tjko/fanpico/images/fanpico-0200-v1.0.jpg

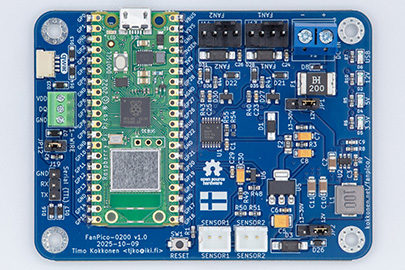
images/fanpico-0200-v1.0.jpg
