tjko/fanpico/images/fanpico-0804D-large.jpg

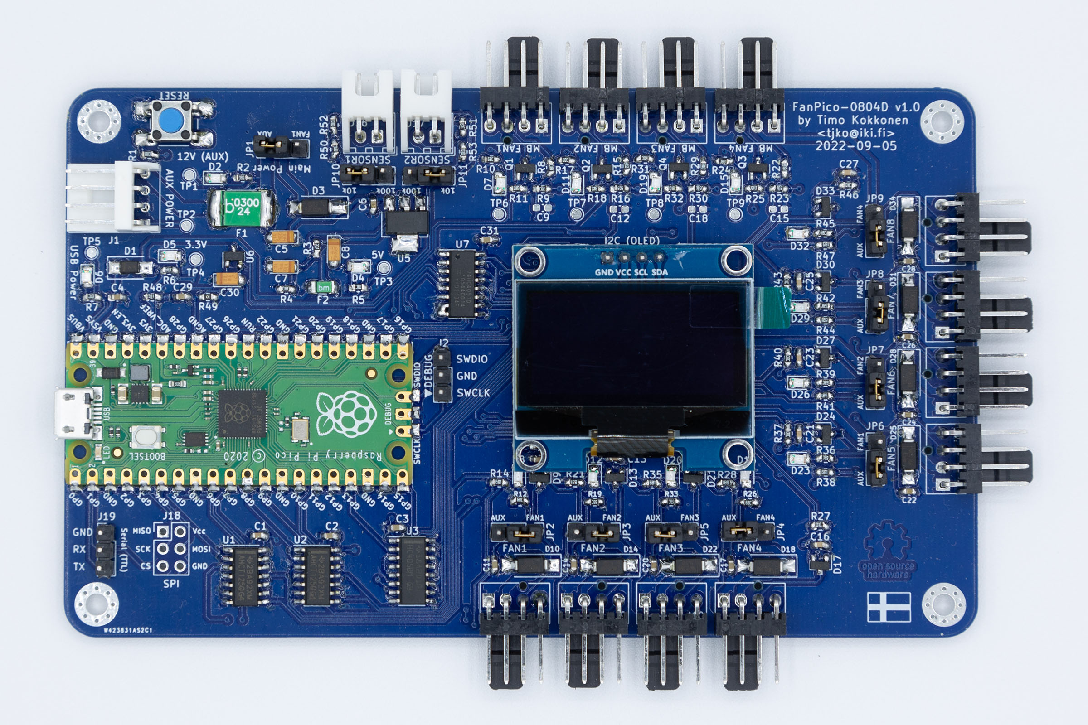
images/fanpico-0804D-large.jpg
