tjko/fanpico/images/fanpico-0804D-v1.2c-large.jpg

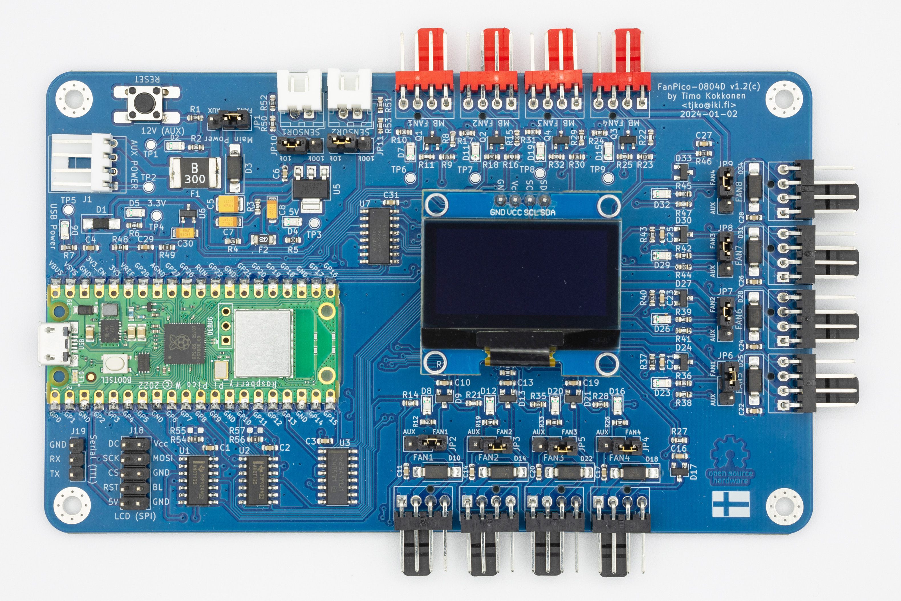
images/fanpico-0804D-v1.2c-large.jpg
