tjko/fanpico/images/fanpico-prototype.jpg

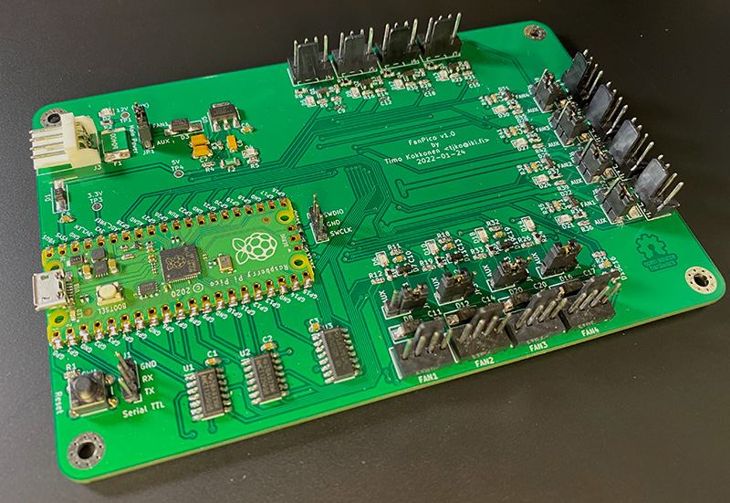
images/fanpico-prototype.jpg
