tjko/fanpico/images/oled-128x64-layout.jpg

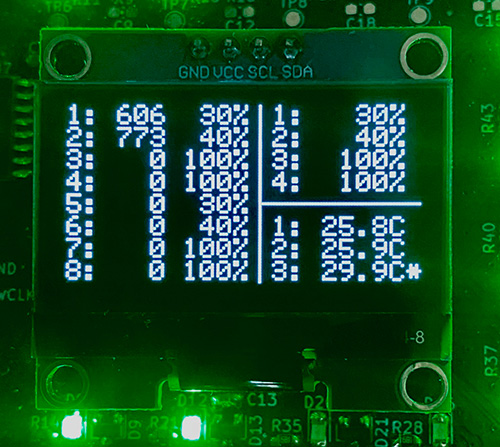
images/oled-128x64-layout.jpg
