tjko/fanpico/images/oled-128x128-layout.jpg

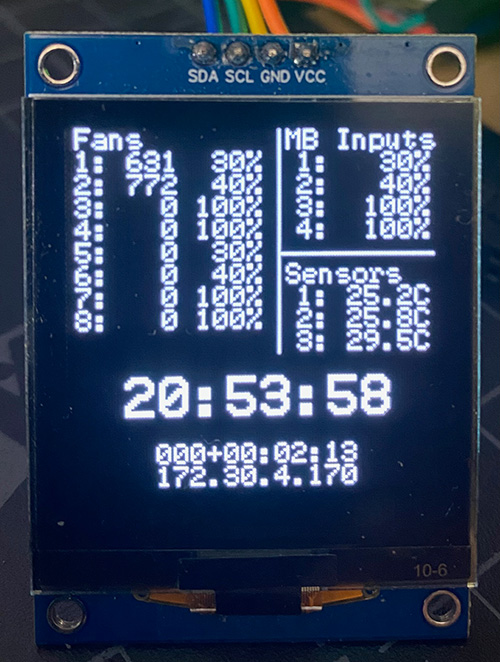
images/oled-128x128-layout.jpg
