tjko/fanpico/images/theme-default-320x240-small.jpg

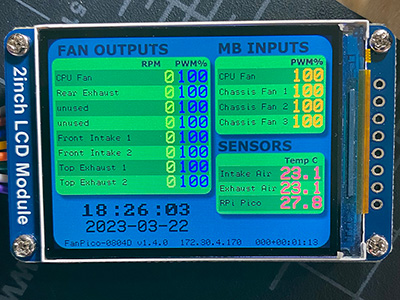
images/theme-default-320x240-small.jpg
