tjko/fanpico/src/themes/default-320x240.png

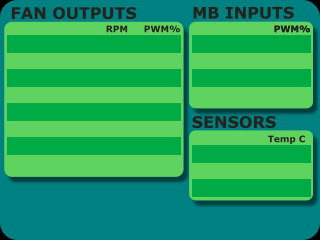
src/themes/default-320x240.png
