tjko/fanpico/src/themes/default-480x320.png

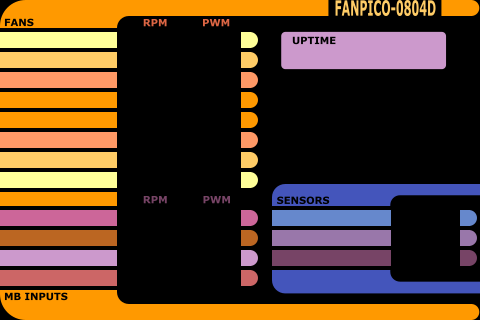
src/themes/default-480x320.png
