tjko/fanpico/src/fanpico_fsdata.c

#include "lwip/apps/fs.h"

static const unsigned char data__404_html[] = {

    /* "/404.html" (10 chars) */
    0x2f,0x34,0x30,0x34,0x2e,0x68,0x74,0x6d,0x6c,0x00,0x00,0x00,

    /* "HTTP/1.0 404 File not found" (29 chars) */
    0x48,0x54,0x54,0x50,0x2f,0x31,0x2e,0x30,0x20,0x34,0x30,0x34,0x20,0x46,0x69,0x6c,
    0x65,0x20,0x6e,0x6f,0x74,0x20,0x66,0x6f,0x75,0x6e,0x64,0x0d,0x0a,

    /* "Server: lwIP/2.2.1 (FanPico)" (30 chars) */
    0x53,0x65,0x72,0x76,0x65,0x72,0x3a,0x20,0x6c,0x77,0x49,0x50,0x2f,0x32,0x2e,0x32,
    0x2e,0x31,0x20,0x28,0x46,0x61,0x6e,0x50,0x69,0x63,0x6f,0x29,0x0d,0x0a,

    /* "Content-Length: 521" (21 chars) */
    0x43,0x6f,0x6e,0x74,0x65,0x6e,0x74,0x2d,0x4c,0x65,0x6e,0x67,0x74,0x68,0x3a,0x20,
    0x35,0x32,0x31,0x0d,0x0a,

    /* "Last-Modified: Tue, 22 Sep 2026 06:35:00 GMT" (46 chars) */
    0x4c,0x61,0x73,0x74,0x2d,0x4d,0x6f,0x64,0x69,0x66,0x69,0x65,0x64,0x3a,0x20,0x54,
    0x75,0x65,0x2c,0x20,0x32,0x32,0x20,0x53,0x65,0x70,0x20,0x32,0x30,0x32,0x36,0x20,
    0x30,0x36,0x3a,0x33,0x35,0x3a,0x30,0x30,0x20,0x47,0x4d,0x54,0x0d,0x0a,

    /* "Content-Type: text/html" (27 chars) */
    0x43,0x6f,0x6e,0x74,0x65,0x6e,0x74,0x2d,0x54,0x79,0x70,0x65,0x3a,0x20,0x74,0x65,
    0x78,0x74,0x2f,0x68,0x74,0x6d,0x6c,0x0d,0x0a,0x0d,0x0a,

    /* raw file data (521 bytes) */
    0x3c,0x68,0x74,0x6d,0x6c,0x3e,0x0a,0x3c,0x68,0x65,0x61,0x64,0x3e,0x3c,0x74,0x69,
    0x74,0x6c,0x65,0x3e,0x46,0x61,0x6e,0x50,0x69,0x63,0x6f,0x3a,0x20,0x45,0x72,0x72,
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
    0x6f,0x2d,0x73,0x74,0x6f,0x72,0x65,0x2c,0x20,0x6e,0x6f,0x2d,0x63,0x61,0x63,0x68,
    0x65,0x2c,0x20,0x6d,0x75,0x73,0x74,0x2d,0x72,0x65,0x76,0x61,0x6c,0x69,0x64,0x61,
    0x74,0x65,0x0d,0x0a,

    /* "Expires: 0" (12) chars) */
    0x45,0x78,0x70,0x69,0x72,0x65,0x73,0x3a,0x20,0x30,0x0d,0x0a,

    /* "Pragma: no-cache" (18) chars) */
    0x50,0x72,0x61,0x67,0x6d,0x61,0x3a,0x20,0x6e,0x6f,0x2d,0x63,0x61,0x63,0x68,0x65,
    0x0d,0x0a,

    /* "Content-Type: application/json" (34 chars) */
    0x43,0x6f,0x6e,0x74,0x65,0x6e,0x74,0x2d,0x54,0x79,0x70,0x65,0x3a,0x20,0x61,0x70,
    0x70,0x6c,0x69,0x63,0x61,0x74,0x69,0x6f,0x6e,0x2f,0x6a,0x73,0x6f,0x6e,0x0d,0x0a,
    0x0d,0x0a,

    /* raw file data (17 bytes) */
    0x3c,0x21,0x2d,0x2d,0x23,0x6a,0x73,0x6f,0x6e,0x73,0x74,0x61,0x74,0x2d,0x2d,0x3e,
    0x0a,
};

const struct fsdata_file file__404_html[] = { {
    NULL,
    data__404_html,
    data__404_html + 12,
    sizeof(data__404_html) - 12,
    FS_FILE_FLAGS_HEADER_INCLUDED | FS_FILE_FLAGS_HEADER_PERSISTENT,
}};

const struct fsdata_file file__fanpico_css[] = { {
    file__404_html,
    data__fanpico_css,
    data__fanpico_css + 16,
    sizeof(data__fanpico_css) - 16,
    FS_FILE_FLAGS_HEADER_INCLUDED | FS_FILE_FLAGS_HEADER_PERSISTENT,
}};

const struct fsdata_file file__img_fanpico_icon_png[] = { {
    file__fanpico_css,
    data__img_fanpico_icon_png,
    data__img_fanpico_icon_png + 24,
    sizeof(data__img_fanpico_icon_png) - 24,
    FS_FILE_FLAGS_HEADER_INCLUDED | FS_FILE_FLAGS_HEADER_PERSISTENT,
}};

const struct fsdata_file file__img_fanpico_png[] = { {
    file__img_fanpico_icon_png,
    data__img_fanpico_png,
    data__img_fanpico_png + 20,
    sizeof(data__img_fanpico_png) - 20,
    FS_FILE_FLAGS_HEADER_INCLUDED | FS_FILE_FLAGS_HEADER_PERSISTENT,
}};

const struct fsdata_file file__index_shtml[] = { {
    file__img_fanpico_png,
    data__index_shtml,
    data__index_shtml + 16,
    sizeof(data__index_shtml) - 16,
    FS_FILE_FLAGS_HEADER_INCLUDED | FS_FILE_FLAGS_SSI,
}};

const struct fsdata_file file__status_csv[] = { {
    file__index_shtml,
    data__status_csv,
    data__status_csv + 12,
    sizeof(data__status_csv) - 12,
    FS_FILE_FLAGS_HEADER_INCLUDED | FS_FILE_FLAGS_SSI,
}};

const struct fsdata_file file__status_json[] = { {
    file__status_csv,
    data__status_json,
    data__status_json + 16,
    sizeof(data__status_json) - 16,
    FS_FILE_FLAGS_HEADER_INCLUDED | FS_FILE_FLAGS_SSI,
}};

#define FS_ROOT file__status_json
#define FS_NUMFILES 7
