tjko/fanpico/src/display_lcd.c

/* display_lcd.c
   Copyright (C) 2022-2023 Timo Kokkonen <tjko@iki.fi>

   SPDX-License-Identifier: GPL-3.0-or-later

   This file is part of FanPico.

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
   You should have received a copy of the GNU General Public License
   along with FanPico. If not, see <https://www.gnu.org/licenses/>.
*/

#include <stdio.h>
#include <stdlib.h>
#include <string.h>
#include <math.h>
#include <assert.h>
#include "pico/stdlib.h"

#include "bb_spi_lcd.h"
#include "fanpico.h"

#if LCD_DISPLAY

static SPILCD lcd;
static uint8_t lcd_found = 0;


/* Macros for converting RGB888 colorspace to RGB565 */

/* Convert 24bit color space to 16bit color space.  */
#define RGB565(rgb) (uint16_t)( ((rgb & 0xf80000) >> 8) | ((rgb & 0xfc00) >> 5) | ((rgb & 0xf8) >> 3) )
/* Generate 16bit color from 8bit RGB components. */
#define RGB565C(r, g, b) (uint16_t)( ((r & 0xf8) << 8) | ((g & 0xfc) << 3) | ((b & 0xf8) >> 3) )


struct lcd_type {
	const char* name;
	int dtype;
	int flags;
	int orientation;
	int32_t spi_freq;
	const uint8_t *custom_init;
	uint32_t custom_init_len;
	int invert_offset;
	int rgb_offset;
};

enum display_field_types {
	INVALID_FIELDTYPE = 0,
	FAN,
	MBFAN,
	SENSOR,
	VSENSOR,
	UPTIME,
	TIME,
	DATE,
	DATE_TIME,
	IP,
	MODEL,
	VERSION,
	MODEL_VERSION,
	DISPLAY_FIELD_TYPE_COUNT
};

enum display_data_types {
	INVALID_DATATYPE = 0,
	LABEL,
	RPM,
	PWM,
	TEMP,
	OTHER,
	DISPLAY_DATA_TYPE_COUNT
};

typedef struct display_field {
	enum display_field_types type;
	enum display_data_types data;
	int id;
	int x;
	int y;
	uint16_t fg;
	uint16_t bg;
	int font;
} display_field_t;

struct display_theme {
	const display_field_t *bg; /* background items, draw only once */
	const display_field_t *fg; /* foreground items */
	const uint8_t *bmp;
	const char* fan_name_fmt;
	uint8_t fan_name_len;
	const char* mbfan_name_fmt;
	uint8_t mbfan_name_len;
	const char* sensor_name_fmt;
	uint8_t sensor_name_len;
	const char* vsensor_name_fmt;
	uint8_t vsensor_name_len;
};

struct display_theme_entry {
	const char *name;
	const struct display_theme *theme_small;  /* 320x240 */
	const struct display_theme *theme_normal; /* 480x320 */
};

typedef struct display_logo {
	const char *name;
	uint16_t width;
	uint16_t height;
	const uint8_t *bmp;
} display_logo_t;


static uint16_t bg_color = RGB565(0x006163);
static uint16_t text_color = RGB565(0x07a3aa);


#include "themes/default-320x240.h"
#include "themes/default-480x320.h"
#if FANPICO_CUSTOM_THEME > 0
#include "themes/custom-320x240.h"
#include "themes/custom-480x320.h"
#endif

const struct display_theme_entry themes[] = {
	{"default", &theme_default_320x240, &theme_default_480x320},
#if FANPICO_CUSTOM_THEME > 0
	{"custom", &theme_custom_320x240, &theme_custom_480x320},
#endif
	{NULL, NULL, NULL}
};


#include "logos/default.h"
#if FANPICO_CUSTOM_LOGO > 0
#include "logos/custom.h"
#endif

const display_logo_t* logos[] = {
	&default_lcd_logo_entry,
#if FANPICO_CUSTOM_LOGO > 0
	&custom_lcd_logo_entry,
#endif
	NULL
};

const struct display_theme *theme = NULL;


const uint8_t waveshare35a[] = {
	1, 0x01,
	LCD_DELAY, 50,
	1, 0x28,
	2, 0xb0, 0x00,
	1, 0x11,
	1, 0x20,   // no-invert [12]
	2, 0x3a, 0x55,
	2, 0x36, 0x28, // RGB mode [18]

	2, 0xc2, 0x44,
	5, 0xc5, 0x00, 0x00, 0x00, 0x00,
	16, 0xe0, 0x0f, 0x1f, 0x1c, 0x0c, 0x0f, 0x08, 0x48, 0x98, 0x37, 0x0a, 0x13, 0x04, 0x11, 0x0d, 0x00,
	16, 0xe1, 0x0f, 0x32, 0x2e, 0x0b, 0x0d, 0x05, 0x47, 0x75, 0x37, 0x06, 0x10, 0x03, 0x24, 0x20, 0x00,
	16, 0xe2, 0x0f, 0x32, 0x2e, 0x0b, 0x0d, 0x05, 0x47, 0x75, 0x37, 0x06, 0x10, 0x03, 0x24, 0x20, 0x00,

	1, 0x11,
	LCD_DELAY, 150,
	1, 0x29,
	LCD_DELAY, 25,
	0
};

const uint8_t waveshare35b[] = {
	1, 0x01,
	LCD_DELAY, 50,
	1, 0x28,
	2, 0xb0, 0x00,
	1, 0x11,
	1, 0x21,   // invert [12]
	2, 0x3a, 0x55,
	2, 0x36, 0x28, // RGB mode [18]

	3, 0xc0, 0x09, 0x09,
	3, 0xc1, 0x41, 0x00,
	3, 0xc5, 0x00, 0x36,
	16, 0xe0, 0x00, 0x2c, 0x2c, 0x0b, 0x0c, 0x04, 0x4c, 0x64, 0x36, 0x03, 0x0e, 0x01, 0x10, 0x01, 0x00,
	16, 0xe1, 0x0f, 0x37, 0x37, 0x0c, 0x0f, 0x05, 0x50, 0x32, 0x36, 0x04, 0x0b, 0x00, 0x19, 0x14, 0x0f,

	1, 0x11,
	LCD_DELAY, 150,
	1, 0x29,
	LCD_DELAY, 25,
	0
};

const uint8_t waveshare35bv2[] = {
	1, 0x01,
	LCD_DELAY, 50,
	1, 0x28,
	2, 0xb0, 0x00,
	1, 0x11,
	1, 0x21,   // invert [12]
	2, 0x3a, 0x55,
	2, 0x36, 0x28, // RGB mode [18]

	2, 0xc2, 0x33,
	4, 0xc5, 0x00, 0x1e, 0x80,
	2, 0xb1, 0xb0,
	16, 0xe0, 0x00, 0x13, 0x18, 0x04, 0x0f, 0x06, 0x3a, 0x56, 0x4d, 0x03, 0x0a, 0x06, 0x30, 0x3e, 0x0f,
	16, 0xe1, 0x00, 0x13, 0x18, 0x01, 0x11, 0x06, 0x38, 0x34, 0x4d, 0x06, 0x0d, 0x0b, 0x31, 0x37, 0x0f,

	1, 0x11,
	LCD_DELAY, 150,
	1, 0x29,
	LCD_DELAY, 25,
	0
};

const struct lcd_type lcd_types[] = {
	/* Generic controllers/panels */
	{"ILI9341", LCD_ILI9341, FLAGS_NONE, LCD_ORIENTATION_90, -1, NULL, 0, -1, -1},
//	{"ILI9342", LCD_ILI9342, FLAGS_NONE, LCD_ORIENTATION_90, -1, NULL, 0, -1, -1},
	{"ST7789", LCD_ST7789, FLAGS_NONE, LCD_ORIENTATION_90, -1, NULL, 0, -1, -1},
	{"ILI9486", LCD_ILI9486, FLAGS_NONE, LCD_ORIENTATION_90, -1, NULL, 0, -1, -1},
	{"HX8357", LCD_HX8357, FLAGS_NONE, LCD_ORIENTATION_90, -1, NULL, 0, -1, -1},

	/* Panel/module specific support */
	{"waveshare35a", LCD_ILI9486, FLAGS_16BIT|FLAGS_SWAP_RB|FLAGS_SWAP_X, LCD_ORIENTATION_90, -1,
	 waveshare35a, sizeof(waveshare35a), 12, 18},
	{"waveshare35b", LCD_ILI9486, FLAGS_16BIT|FLAGS_SWAP_RB|FLAGS_SWAP_X, LCD_ORIENTATION_90, -1,
	 waveshare35b, sizeof(waveshare35b), 12, 18},
	{"waveshare35bv2", LCD_ILI9486, FLAGS_16BIT|FLAGS_SWAP_RB|FLAGS_SWAP_X, LCD_ORIENTATION_90, -1,
	 waveshare35bv2, sizeof(waveshare35bv2), 12, 18},

	{NULL, -1, -1, -1, -1, NULL, 0, -1, -1}
};

void draw_rounded_box(SPILCD *lcd, uint16_t x, uint16_t y, uint16_t width, uint16_t height, uint8_t r, uint16_t color)
{
	spilcdRectangle(lcd, x + r, y, width - (2 * r), r, color, color, 1, DRAW_TO_LCD);
	spilcdRectangle(lcd, x, y + r, width, height - (2 * r), color, color, 1, DRAW_TO_LCD);
	spilcdRectangle(lcd, x + r, y + height - r, width - (2 * r), r, color, color, 1, DRAW_TO_LCD);

	spilcdEllipse(lcd, x + r, y + r, r, r, color, 1, DRAW_TO_LCD);
	spilcdEllipse(lcd, x + width - r - 1, y + r, r, r, color, 1, DRAW_TO_LCD);
	spilcdEllipse(lcd, x + r, y + height - r, r, r, color, 1, DRAW_TO_LCD);
	spilcdEllipse(lcd, x + width - r - 1, y + height - r, r, r, color, 1, DRAW_TO_LCD);
}

void lcd_display_init()
{
	int dtype = LCD_INVALID;
	int flags = FLAGS_NONE;
	int orientation = LCD_ORIENTATION_90;
	int32_t spi_freq = SPI_DEFAULT_SPEED;
	const char *lcd_name = "";
	int val;
	char *args, *tok, *saveptr;
	int theme_idx;


	if (!cfg)
		return;
	memset(&lcd, 0, sizeof(lcd));

	args = strdup(cfg->display_type);
	if (!args)
		return;
	tok = strtok_r(args, ",", &saveptr);
	while (tok) {
		if (!strncmp(tok,"lcd=", 4)) {
			char *t = tok + 4;
			int i = 0;
			while (lcd_types[i].name) {
				const struct lcd_type *l = &lcd_types[i];
				if (!strcmp(l->name, t)) {
					lcd_name = l->name;
					dtype = l->dtype;
					if (l->flags >= 0)
						flags = l->flags;
					if (l->orientation >= 0)
						orientation = l->orientation;
					if (l->spi_freq >= 0)
						spi_freq = l->spi_freq;
					if (l->custom_init)
						spilcdCustomInit(&lcd, l->custom_init, l->custom_init_len,
								l->invert_offset, l->rgb_offset);
					break;
				}
				i++;
			}
		}
		else if (!strncmp(tok, "rotate=", 7)) {
			if (str_to_int(tok + 7, &val, 10)) {
				switch(val) {
				case 90:
					orientation = LCD_ORIENTATION_90;
					break;
				case 180:
					orientation = LCD_ORIENTATION_180;
					break;
				case 270:
					orientation = LCD_ORIENTATION_270;
					break;
				default:
					orientation = LCD_ORIENTATION_0;
				}
			}
		}
		else if (!strncmp(tok, "spifreq=", 8)) {
			if (str_to_int(tok + 8, &val, 10)) {
				if (val > 0 && val < 1000) {
					spi_freq = val * 1000 * 1000;
				}
				else if (val >= 1000) {
					spi_freq = val;
				}
			}
		}
		else if (!strncmp(tok, "invert", 6))
			flags ^= FLAGS_INVERT;
		else if (!strncmp(tok, "swapcolors", 10))
			flags ^= FLAGS_SWAP_RB;
		else if (!strncmp(tok, "16bit", 5))
			flags |= FLAGS_16BIT;

		tok = strtok_r(NULL, ",", &saveptr);
	}
	free(args);

	if (dtype == LCD_INVALID) {
		log_msg(LOG_NOTICE, "No LCD type configured!");
		return;
	}

	lcd_found = 1;

	log_msg(LOG_NOTICE, "Initializing LCD display...");
	log_msg(LOG_INFO, "SPI Frequency: %ld Hz", spi_freq);

	int res = spilcdInit(&lcd, dtype, flags, spi_freq,
		CS_PIN, DC_PIN, LCD_RESET_PIN, LCD_LIGHT_PIN,
		MISO_PIN, MOSI_PIN, SCK_PIN);
	log_msg(LOG_DEBUG, "spilcdInit(): %d", res);

	spilcdSetOrientation(&lcd, orientation);
	spilcdFill(&lcd, 0, DRAW_TO_LCD);

	log_msg(LOG_NOTICE, "LCD display: %s %dx%d",
		lcd_name,
		lcd.iCurrentWidth, lcd.iCurrentHeight);


	/* Draw logo to screen */
	const display_logo_t *logo = logos[0]; /* Default logo */
	if (strlen(cfg->display_logo) > 0) {
		int idx = 0;
		while (logos[idx]) {
			if (!strncmp(cfg->display_logo, logos[idx]->name, sizeof(cfg->display_logo))) {
				logo = logos[idx];
				break;
			}
			idx++;
		}
	}

	int w_c = lcd.iCurrentWidth / 2;
	int h_c = lcd.iCurrentHeight / 2;
	spilcdDrawBMP(&lcd, logo->bmp,
		w_c - (logo->width / 2),
		h_c - ((logo->height + 80) / 2),
		0, -1, DRAW_TO_LCD);
	h_c += logo->height / 2;
	spilcdWriteString(&lcd, w_c - 100, h_c, "FanPico-" FANPICO_MODEL, text_color, 0, FONT_16x16, DRAW_TO_LCD);
	spilcdWriteString(&lcd, w_c - 40, h_c + 25, "v" FANPICO_VERSION, text_color, 0, FONT_16x16, DRAW_TO_LCD);
	spilcdWriteString(&lcd, w_c - 50, h_c + 55, "Initializing...", text_color, 0, FONT_8x8, DRAW_TO_LCD);

	/* Select theme to use... */
	theme_idx = 0; /* use first theme by default... */
	if (strlen(cfg->display_theme) > 0) {
		int i = 0;
		while (themes[i].name) {
			if (!strcmp(themes[i].name, cfg->display_theme)) {
				theme_idx = i;
				break;
			}
			i++;
		}
	}
	theme = (lcd.iCurrentWidth >= 480 ? themes[theme_idx].theme_normal : themes[theme_idx].theme_small);
	log_msg(LOG_INFO, "LCD theme: %s", themes[theme_idx].name);
}

void lcd_clear_display()
{
	if (!lcd_found)
		return;

	spilcdFill(&lcd, 0, DRAW_TO_LCD);
}

void draw_fields(const struct fanpico_state *state, const struct fanpico_config *conf, const struct display_theme *theme, int mode)
{
	int i = 0;
	char buf[64];
	double val;
	struct tm t;
	const display_field_t *list;

	list = (mode ? theme->fg : theme->bg);


	while (list[i].type > INVALID_FIELDTYPE && list[i].type < DISPLAY_FIELD_TYPE_COUNT) {
		const display_field_t *f = &list[i];

		buf[0] = 0;
		switch (f->data) {

		case LABEL:
			switch (f->type) {

			case FAN:
				snprintf(buf, theme->fan_name_len + 1, theme->fan_name_fmt,
					conf->fans[f->id].name);
				break;

			case MBFAN:
				snprintf(buf, theme->mbfan_name_len + 1, theme->mbfan_name_fmt,
					conf->mbfans[f->id].name);
				break;

			case SENSOR:
				snprintf(buf, theme->sensor_name_len + 1, theme->sensor_name_fmt,
					conf->sensors[f->id].name);
				break;

			case VSENSOR:
				snprintf(buf, theme->vsensor_name_len + 1, theme->vsensor_name_fmt,
					conf->vsensors[f->id].name);
				break;

			case MODEL_VERSION:
				snprintf(buf, sizeof(buf), "%s",
					"FanPico-" FANPICO_MODEL " v" FANPICO_VERSION);
				break;

			default:
				break;
			}
			break;

		case RPM:
			switch (f->type) {

			case FAN:
				val = state->fan_freq[f->id] * 60 / conf->fans[f->id].rpm_factor;
				break;

			case MBFAN:
				val = state->mbfan_freq[f->id] * 60 / conf->mbfans[f->id].rpm_factor;
				break;

			default:
				val = 0.0;
			}
			snprintf(buf, 5, "%4.0lf", val);
			break;

		case PWM:
			switch (f->type) {
			case FAN:
				val = state->fan_duty[f->id];
				break;
			case MBFAN:
				val = state->mbfan_duty[f->id];
				break;
			default:
				val = 0.0;
			}
			snprintf(buf, 4, "%3.0lf", val);
			break;

		case TEMP:
			switch (f->type) {
			case SENSOR:
				val = state->temp[f->id];
				break;
			case VSENSOR:
				val = state->vtemp[f->id];
				break;
			default:
				val = 0.0;
			}
			snprintf(buf, 5, "%2.1lf", val);
			break;

		case OTHER:
			switch (f->type) {
			case IP: {
				const char* net_ip = network_ip();
				snprintf(buf, 16, "%15s", (net_ip ? net_ip : ""));
				break;
			}
			case DATE_TIME:
				if (rtc_get_tm(&t)) {
					snprintf(buf, sizeof(buf), "%04d-%02d-%02d %02d:%02d:%02d",
						t.tm_year + 1900, t.tm_mon + 1, t.tm_mday,
						t.tm_hour, t.tm_min, t.tm_sec);
				}
				break;
			case DATE:
				if (rtc_get_tm(&t)) {
					snprintf(buf, sizeof(buf), "%04d-%02d-%02d",
						t.tm_year + 1900, t.tm_mon + 1, t.tm_mday);
				}
				break;
			case TIME:
				if (rtc_get_tm(&t)) {
					snprintf(buf, sizeof(buf), "%02d:%02d:%02d",
						t.tm_hour, t.tm_min, t.tm_sec);
				}
				break;
			case UPTIME:
			        {
					uint32_t secs = to_us_since_boot(get_absolute_time()) / 1000000;
					uint32_t mins =  secs / 60;
					uint32_t hours = mins / 60;
					uint32_t days = hours / 24;

					snprintf(buf, 13, "%03lu+%02lu:%02lu:%02lu",
						days % 1000,
						hours % 24,
						mins % 60,
						secs % 60);
			        }
				break;

			default:
				break;
			}
			break;

		default:
			buf[0] = 0;
		}

		if (strlen(buf) > 0)
			spilcdWriteString(&lcd, f->x, f->y, buf, f->fg, f->bg, f->font, DRAW_TO_LCD);

		i++;
	}
}

void lcd_display_status(const struct fanpico_state *state,
	const struct fanpico_config *conf)
{
	static uint8_t bg_drawn = 0;


	if (!lcd_found || !state)
		return;

	if (!bg_drawn) {
		/* draw background graphics only once... */
		bg_drawn = 1;
		//spilcdRectangle(&lcd, 0, 0, lcd.iCurrentWidth -1, lcd.iCurrentHeight - 1, 0xffff, 0xffff, 0, DRAW_TO_LCD);

		if (theme->bmp) {
			spilcdDrawBMP(&lcd, theme->bmp, 0, 0,	0, -1, DRAW_TO_LCD);
			draw_fields(state, conf, theme, 0);
			return;
		} else {
			spilcdFill(&lcd, 0x0000, DRAW_TO_LCD);
			if (bg_color != 0)
				draw_rounded_box(&lcd,
						0, 0,
						lcd.iCurrentWidth - 1, lcd.iCurrentHeight -1 ,
						10, bg_color);
			draw_fields(state, conf, theme, 0);
		}
	}

	draw_fields(state, conf, theme, 1);
}

void lcd_display_message(int rows, const char **text_lines)
{
	int screen_rows = lcd.iCurrentHeight / 16;
	int start_row = 0;

	if (!lcd_found)
		return;

	lcd_clear_display();

	if (rows < screen_rows) {
		start_row = (screen_rows - rows) / 2;
	}

	for(int i = 0; i < rows; i++) {
		int row = start_row + i;
		char *text = (char*)text_lines[i];

		if (row >= screen_rows)
			break;

		spilcdWriteString(&lcd, 0, row * 16, (text ? text : ""), 65535, 0, FONT_12x16, DRAW_TO_LCD);
	}
}

#endif
/* eod :-) */
