tjko/fanpico/src/boards/0804.h

/* boards/0804.h */


#define FANPICO_MODEL     "0804"

#define FAN_COUNT     8   /* Number of Fan outputs on the board */
#define MBFAN_COUNT   4   /* Number of (Motherboard) Fan inputs on the board */
#define SENSOR_COUNT  3   /* Number of sensor inputs on the board */

#define LED_PIN 25


/* Pins for Fan Signals */

#define TACHO_READ_MULTIPLEX 0

/* pins for multiplexed read */
#define FAN_TACHO_READ_PIN    -1
#define FAN_TACHO_READ_S0_PIN -1
#define FAN_TACHO_READ_S1_PIN -1
#define FAN_TACHO_READ_S2_PIN -1
/* pins for direct read / multiplexer ports (if multiplexer in use) */
#define FAN1_TACHO_READ_PIN 2
#define FAN2_TACHO_READ_PIN 3
#define FAN3_TACHO_READ_PIN 20
#define FAN4_TACHO_READ_PIN 21
#define FAN5_TACHO_READ_PIN 22
#define FAN6_TACHO_READ_PIN 26
#define FAN7_TACHO_READ_PIN 1
#define FAN8_TACHO_READ_PIN 0

#define FAN1_PWM_GEN_PIN 4  /* PWM2A */
#define FAN2_PWM_GEN_PIN 5  /* PWM2B */
#define FAN3_PWM_GEN_PIN 6  /* PWM3A */
#define FAN4_PWM_GEN_PIN 7  /* PWM3B */
#define FAN5_PWM_GEN_PIN 8  /* PWM4A */
#define FAN6_PWM_GEN_PIN 9  /* PWM4B */
#define FAN7_PWM_GEN_PIN 10 /* PWM5A */
#define FAN8_PWM_GEN_PIN 11 /* PWM5B */


/* Pins for Motherboar Fan Connector Signals */

#define MBFAN1_TACHO_GEN_PIN 12
#define MBFAN2_TACHO_GEN_PIN 14
#define MBFAN3_TACHO_GEN_PIN 16
#define MBFAN4_TACHO_GEN_PIN 18

#define MBFAN1_PWM_READ_PIN 13 /* PWM6B */
#define MBFAN2_PWM_READ_PIN 15 /* PWM7B */
#define MBFAN3_PWM_READ_PIN 17 /* PWM0B */
#define MBFAN4_PWM_READ_PIN 19 /* PWM1B */


/* Pins for temperature sensors */

#define SENSOR1_READ_PIN  27  /* ADC1 / GPIO27 */
#define SENSOR2_READ_PIN  28  /* ADC2 / GPIO28 */

#define SENSOR1_READ_ADC  1  /* ADC1 / GPIO27 */
#define SENSOR2_READ_ADC  2  /* ADC2 / GPIO28 */
#define SENSOR3_READ_ADC  ADC_TEMPERATURE_CHANNEL_NUM  /* Internal Temperature sensor */


/* Interface Pins */

/* I2C */
#define I2C_HW    1  /* 1=i2c0, 2=i2c1, 0=bitbang... */
#define SDA_PIN  -1
#define SCL_PIN  -1

/* Serial */
#define TX_PIN   -1
#define RX_PIN   -1

/* SPI */
#define SPI_SHARED     1 /* 0 = dedicated pins, 1 = shared with serial/i2c */
#define SCK_PIN       -1
#define MOSI_PIN      -1
#define MISO_PIN      -1
#define CS_PIN        -1

#define DC_PIN        -1
#define LCD_RESET_PIN -1
#define LCD_LIGHT_PIN -1

#define ONEWIRE_SUPPORT 0
#define ONEWIRE_SHARED  1 /* 0 = dedicated pins, 1 = shared with serial */
#define ONEWIRE_PIN    -1
