tjko/fanpico/src/psram.c

/* psram.c
   Copyright (C) 2025 Timo Kokkonen <tjko@iki.fi>

   SPDX-License-Identifier: GPL-3.0-or-later

   This file is part of FanPico.

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
   You should have received a copy of the GNU General Public License
   along with FanPico. If not, see <https://www.gnu.org/licenses/>.
*/

#include <stdio.h>
#include <string.h>
#if !PICO_RP2040
#include "hardware/structs/qmi.h"
#endif
#include "hardware/structs/ioqspi.h"
#include "hardware/structs/xip_ctrl.h"
#include "hardware/gpio.h"
#include "hardware/clocks.h"
#include "hardware/sync.h"

#include "psram.h"


/* NOTE! This code tries to minimize RAM usage.
   Currently only 324 bytes of RAM is used for static variables
   and in-memory functions. */


/* PSRAM Manufacturer IDs */
#define MFID_APMEMORY         0x0d
#define MFID_ISSI             0x9d

/* PSRAM Command Codes */
#define CMD_READ              0x03
#define CMD_FAST_READ         0x0b
#define CMD_QUAD_READ         0xeb
#define CMD_WRITE             0x02
#define CMD_QUAD_WRITE        0x38
#define CMD_ENTER_QPI_MODE    0x35
#define CMD_EXIT_QPI_MODE     0xf5
#define CMD_RESET_ENABLE      0x66
#define CMD_RESET             0x99
#define CMD_SET_BURST_LEN     0xc0
#define CMD_READ_ID           0x9f
#define CMD_DPD_MODE_ENTRY    0xb9

/* KGD (Known Good Die) Test */
#define KGD_FAIL              0x55
#define KGD_PASS              0x5d


/* Speed of SPI mode access is not important. It just needs to be "slow enough"
   to reliably send "direct" mode commands during setup. */
#define PSRAM_MAX_CSR_CLK                  5000000 /* 5MHz max clock for "direct" mode */


struct psram_type_t {
	uint8_t mfid;
	const char* mfname;
	uint32_t max_clk;
	uint64_t max_select_fs;
	uint32_t min_deselect_fs;
	int min_deselect_cs;
};


/* PSRAM timings by chip manufacturer */

static const struct psram_type_t psram_chip_types[] = {
	/* ID             Name        Max Clk (Mhz)   tCEM (fs)    tCPM (fs)   tCPM (cs) */
	{ MFID_APMEMORY, "AP Memory",     109000000,  8000000000,   18000000,         -1 },
	{ MFID_ISSI,     "ISSI",          104000000,  4000000000,          0,          1 },
	{ 0,             "Unknown",       109000000,  8000000000,   50000000,         -1 }
};


#ifdef PSRAM_CS_PIN

static size_t psram_sz = 0;
static psram_id_t psram_id = { 0 };


static inline void csr_busy_wait()
{
	/* Wait for BUSY flag to clear */
	while((qmi_hw->direct_csr & QMI_DIRECT_CSR_BUSY_BITS)) {
		tight_loop_contents();
	};
}

static inline void csr_txempty_wait()
{
	/* Wait for TXEMPTY flag to get set */
	while((qmi_hw->direct_csr & QMI_DIRECT_CSR_TXEMPTY_BITS) == 0) {
		tight_loop_contents();
	};
}

static inline void csr_enable_direct_mode(uint8_t csr_clkdiv)
{
	/* Enable CRS mode and set clock divider */
	qmi_hw->direct_csr = csr_clkdiv << QMI_DIRECT_CSR_CLKDIV_LSB | QMI_DIRECT_CSR_EN_BITS;
	csr_busy_wait();
}

static inline void csr_disable_direct_mode()
{
	/* Disable direct mode */
	hw_clear_bits(&qmi_hw->direct_csr, QMI_DIRECT_CSR_EN_BITS | QMI_DIRECT_CSR_ASSERT_CS1N_BITS);
}


static void __no_inline_not_in_flash_func(csr_send_command)(uint32_t cmd, uint16_t *rx)
{
	uint16_t res;

	hw_set_bits(&qmi_hw->direct_csr, QMI_DIRECT_CSR_ASSERT_CS1N_BITS);
	qmi_hw->direct_tx = cmd;
	csr_txempty_wait();
	csr_busy_wait();
	res = qmi_hw->direct_rx;
	hw_clear_bits(&qmi_hw->direct_csr, QMI_DIRECT_CSR_ASSERT_CS1N_BITS);
	if (rx)
		*rx = res;
}


static void __no_inline_not_in_flash_func(psram_read_id)(uint8_t csr_clkdiv, uint8_t *buffer)
{
	uint32_t saved_ints = save_and_disable_interrupts();
	uint8_t rx;

	csr_enable_direct_mode(csr_clkdiv);

	/* Send 'Exit QPI mode' command to make sure chip is in SPI mode */
	csr_send_command(
		QMI_DIRECT_TX_OE_BITS |
		QMI_DIRECT_TX_IWIDTH_VALUE_Q << QMI_DIRECT_TX_IWIDTH_LSB |
		CMD_EXIT_QPI_MODE, NULL);

	/* Send 'Read ID' command (this only works in SPI mode) */
	hw_set_bits(&qmi_hw->direct_csr, QMI_DIRECT_CSR_ASSERT_CS1N_BITS);
	for (int i = 0; i < (4 + 8); i++) {
		qmi_hw->direct_tx = (i == 0 ? CMD_READ_ID : 0x00);
		csr_txempty_wait();
		csr_busy_wait();
		rx = qmi_hw->direct_rx;
		if (i >= 4)
			buffer[i - 4] = rx;
	}

	csr_disable_direct_mode();

	restore_interrupts(saved_ints);
}


static void __no_inline_not_in_flash_func(psram_qmi_setup)(uint8_t clkdiv, uint8_t csr_clkdiv,
							uint8_t max_select, uint8_t min_deselect,
							uint8_t rxdelay)
{
	uint32_t saved_ints = save_and_disable_interrupts();


	/* Reset PSRAM chip and set it in QPI Mode */

	csr_enable_direct_mode(csr_clkdiv);
	csr_send_command(CMD_RESET_ENABLE, NULL);
	csr_send_command(CMD_RESET, NULL);
	csr_send_command(CMD_ENTER_QPI_MODE, NULL);
	csr_disable_direct_mode();


	/* Configure QSPI Memory Interface */

	/* Set M1_TIMING register */
	qmi_hw->m[1].timing = (
		1                                  << QMI_M1_TIMING_COOLDOWN_LSB |
		QMI_M1_TIMING_PAGEBREAK_VALUE_1024 << QMI_M1_TIMING_PAGEBREAK_LSB |
		0                                  << QMI_M1_TIMING_SELECT_SETUP_LSB |
		3                                  << QMI_M1_TIMING_SELECT_HOLD_LSB |
		max_select                         << QMI_M1_TIMING_MAX_SELECT_LSB |
		min_deselect                       << QMI_M1_TIMING_MIN_DESELECT_LSB |
		rxdelay                            << QMI_M1_TIMING_RXDELAY_LSB |
		clkdiv                             << QMI_M1_TIMING_CLKDIV_LSB
		);

	/* Set M1_RFMT / M1_RCMD registers */
	qmi_hw->m[1].rfmt = (
		0                                  << QMI_M1_RFMT_DTR_LSB |
		QMI_M1_RFMT_DUMMY_LEN_VALUE_24     << QMI_M1_RFMT_DUMMY_LEN_LSB |
		QMI_M1_RFMT_SUFFIX_LEN_VALUE_NONE  << QMI_M1_RFMT_SUFFIX_LEN_LSB |
		QMI_M1_RFMT_PREFIX_LEN_VALUE_8     << QMI_M1_RFMT_PREFIX_LEN_LSB |
		QMI_M1_RFMT_DATA_WIDTH_VALUE_Q     << QMI_M1_RFMT_DATA_WIDTH_LSB |
		QMI_M1_RFMT_DUMMY_WIDTH_VALUE_Q    << QMI_M1_RFMT_DUMMY_WIDTH_LSB |
		QMI_M1_RFMT_SUFFIX_WIDTH_VALUE_Q   << QMI_M1_RFMT_SUFFIX_WIDTH_LSB |
		QMI_M1_RFMT_ADDR_WIDTH_VALUE_Q     << QMI_M1_RFMT_ADDR_WIDTH_LSB |
		QMI_M1_RFMT_PREFIX_WIDTH_VALUE_Q   << QMI_M1_RFMT_PREFIX_WIDTH_LSB
		);
	qmi_hw->m[1].rcmd = (
		0                                  << QMI_M1_RCMD_SUFFIX_LSB |
		CMD_QUAD_READ                      << QMI_M1_RCMD_PREFIX_LSB
		);

	/* Set M1_WFMT / M1_WCMD registers */
	qmi_hw->m[1].wfmt = (
		0                                  << QMI_M1_WFMT_DTR_LSB |
		QMI_M1_WFMT_DUMMY_LEN_VALUE_NONE   << QMI_M1_WFMT_DUMMY_LEN_LSB |
		QMI_M1_WFMT_SUFFIX_LEN_VALUE_NONE  << QMI_M1_WFMT_SUFFIX_LEN_LSB |
		QMI_M1_WFMT_PREFIX_LEN_VALUE_8     << QMI_M1_WFMT_PREFIX_LEN_LSB |
		QMI_M1_WFMT_DATA_WIDTH_VALUE_Q     << QMI_M1_WFMT_DATA_WIDTH_LSB |
		QMI_M1_WFMT_DUMMY_WIDTH_VALUE_Q    << QMI_M1_WFMT_DUMMY_WIDTH_LSB |
		QMI_M1_WFMT_SUFFIX_WIDTH_VALUE_Q   << QMI_M1_WFMT_SUFFIX_WIDTH_LSB |
		QMI_M1_WFMT_ADDR_WIDTH_VALUE_Q     << QMI_M1_WFMT_ADDR_WIDTH_LSB |
		QMI_M1_WFMT_PREFIX_WIDTH_VALUE_Q   << QMI_M1_WFMT_PREFIX_WIDTH_LSB
		);
	qmi_hw->m[1].wcmd = (
		0                                  << QMI_M1_WCMD_SUFFIX_LSB |
		CMD_QUAD_WRITE                     << QMI_M1_WCMD_PREFIX_LSB
		);


	restore_interrupts(saved_ints);

	/* Enable writes to PSRAM (XIP) memory region */
	hw_set_bits(&xip_ctrl_hw->ctrl, XIP_CTRL_WRITABLE_M1_BITS);
}


static bool psram_is_writable(void *base_addr)
{
	volatile uint32_t *psram = (volatile uint32_t*)base_addr;
	volatile uint32_t rb_1, rb_2;

	/* Test if we can write to PSRAM... */
	psram[0] = 0xdeadc0de;
	rb_1 = psram[0];
	psram[0] = 0;
	rb_2 = psram[0];

	return (rb_1 == 0xdeadc0de && rb_2 == 0) ? true : false;
}


static bool psram_check_size(void *base_addr, uint32_t size)
{
	volatile uint32_t *psram = (volatile uint32_t*)base_addr;
	uint32_t psram_len = size / sizeof(uint32_t);


	if (size > PSRAM_WINDOW_SIZE)
		return false;
	if (size == PSRAM_WINDOW_SIZE)
		return true;

	/* Clear out beginning of the PSRAM */
	psram[0] = 0;

	/* Write past the 'end' of PSRAM */
	psram[psram_len] = 0xc0ffee42;

	/* Check if we see the earlier write at the beginning of the PSRAM. */
	if (psram[0] == 0xc0ffee42) {
		psram[0] = 0;
		return true;
	}

	psram[psram_len] = 0;
	return false;
}


static int psram_init(int pin, bool clear_memory)
{
	const struct psram_type_t *chip = psram_chip_types;
	uint32_t sys_clk = clock_get_hz(clk_sys);
	uint32_t clock_period_fs = 1000000000000000ll / sys_clk;
	uint8_t csr_clkdiv = (sys_clk + PSRAM_MAX_CSR_CLK - 1) / PSRAM_MAX_CSR_CLK;
	int ret = 0;


	psram_sz = 0;
	if (pin < 0)
		return -1;

	/* Configure GPIO pin */
	gpio_set_function(pin, GPIO_FUNC_XIP_CS1);

	/* Check if PSRAM chip is present */
	psram_read_id(csr_clkdiv, (uint8_t*)&psram_id);
	if (psram_id.kgd != KGD_PASS) {
		/* No PSRAM chip found */
		return -2;
	}

	/* Lookup PSRAM Timings */
	while (chip->mfid && chip->mfid != psram_id.mfid)
		chip++;

	/* Density EID[47:45] (encoding of this is manufacturer specific)  */
	uint8_t density = (psram_id.eid[0] >> 5);

	/* Try to determine PSRAM size */
	switch (psram_id.mfid) {
	case MFID_APMEMORY:
		psram_sz = 2;
		if (density == 1)
			psram_sz = 4;
		else if (density == 2)
			psram_sz = 8;
		break;
	case MFID_ISSI:
		psram_sz = 1;
		if (density == 1)
			psram_sz = 2;
		else if (density == 2)
			psram_sz = 4;
		break;
	default:
		psram_sz = 1;
	}

	/* Convert size from megabytes to bytes */
	psram_sz <<= 20;


	/* Calculate clock divider to get as close as possible to the max supported clock speed */
	uint8_t clkdiv = (sys_clk + chip->max_clk - 1) / chip->max_clk;

	/* Calculate PSRAM timings */
	uint8_t max_select = (chip->max_select_fs >> 6) / clock_period_fs;
	uint8_t min_deselect = (chip->min_deselect_fs + clock_period_fs - 1) / clock_period_fs;
	if (chip->min_deselect_cs >= 0)
		min_deselect = chip->min_deselect_cs;
	uint8_t rxdelay = 1 + (sys_clk > 150000000 ? clkdiv : 1);


	/* Enable PSRAM */
	psram_qmi_setup(clkdiv , csr_clkdiv, max_select, min_deselect, rxdelay);


	/* Test that we can write to PSRAM */
	if (!psram_is_writable((void*)PSRAM_NOCACHE_BASE)) {
		/* Cannot write to PSRAM! */
		psram_sz = 0;
		return -3;
	}

	/* Validate PSRAM size determined from the Read ID command */
	uint32_t actual_size = PSRAM_WINDOW_SIZE;
	for (uint32_t i = 1 << 20; i < PSRAM_WINDOW_SIZE;  i <<= 1) {
		if (psram_check_size((void*)PSRAM_NOCACHE_BASE, i)) {
			actual_size = i;
			break;
		}
	}
	if (actual_size != psram_sz) {
		/* PSRAM size mismatch. Use detected memory size. */
		psram_sz = actual_size;
		ret = -4;
	}

	/* Clear PSRAM */
	if (clear_memory)
		memset((void*)PSRAM_NOCACHE_BASE, 0, psram_sz);

	return ret;
}
#endif


void psram_setup()
{
#ifdef PSRAM_CS_PIN
	int res = psram_init(PSRAM_CS_PIN, true);
	if (res == -3) {
		printf("PSRAM: Cannot write to PSRAM!\n");
	}
	else if (res == -4) {
		printf("PSRAM: Memory size mismatch!\n");
	}
#endif
}


size_t psram_size()
{
#ifdef PSRAM_CS_PIN
	return psram_sz;
#else
	return 0;
#endif
}


const psram_id_t* psram_get_id()
{
#ifdef PSRAM_CS_PIN
	return (const psram_id_t*)&psram_id;
#else
	return NULL;
#endif
}


const char* psram_get_manufacturer(uint8_t mfid)
{
	const struct psram_type_t *chip = psram_chip_types;

	while (chip->mfid && chip->mfid != mfid)
		chip++;

	return chip->mfname;
}
