tjko/fanpico/src/pulse_len.c

/* pulse_len.c
   Copyright (C) 2021-2024 Timo Kokkonen <tjko@iki.fi>

   SPDX-License-Identifier: GPL-3.0-or-later

   This file is part of FanPico.

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
   You should have received a copy of the GNU General Public License
   along with FanPico. If not, see <https://www.gnu.org/licenses/>.
*/

#include "pico/stdlib.h"
#include "hardware/gpio.h"


/*
 * Functions for measuring pulses on GPIO pins.
 */


/* pulse_measure - measure pulse length or interval from a GPIO
 *
 * This function does not use interrupts. On a RP2040 this was observed
 * to achieve about +/- 1 microsecond accuracy, based on quick test with
 * a signal generator. Function works down to about 5 microsecond pulse
 * lengths.
 *
 *     pin: GPIO input pin
 *    type: true=measure HIGH pulse, false = measure LOW pulse
 *    mode: true=measure pulse length, false = measure time between two pulses
 * timeout: timeout in ms, return 0 if no pulse seen before timeout
 *
 */
uint64_t pulse_measure(int pin, bool type, bool mode, uint32_t timeout_ms)
{
	absolute_time_t start = get_absolute_time();
	absolute_time_t pulse_start = start;
	absolute_time_t now;
	uint64_t timeout = timeout_ms * 1000;
	int state = 0;
	bool in;


	do {
		in = gpio_get(pin);
		now = get_absolute_time();

		if (state == 0 && in == !type) {
			/* wait until previous pulse is done... */
			state = 1;
		}
		else if (state == 1 && in == type) {
			/* pulse start detected */
			state = 2;
			pulse_start = now;
		}
		else if (state == 2 && in == !type) {
			/* pulse end detected */
			if (mode) {
				return absolute_time_diff_us(pulse_start, now);
			} else {
				state = 3;
			}
		}
		else if (state == 3 && in == type) {
			/* next pulse start detected */
			return absolute_time_diff_us(pulse_start, now);
		}
	} while (absolute_time_diff_us(start, now) <= timeout);

	return 0;
}

/* pulseIn -  Arduino style wrapper for pulse_measure
 */
uint64_t pulseIn(int gpio, int value, uint32_t timeout_ms)
{
	return pulse_measure(gpio, (value ? true : false), true, timeout_ms);
}



uint pulse_pin = 0;
volatile uint32_t pulse_counter = 0;
volatile bool measure_complete = false;
absolute_time_t pulse_start;
absolute_time_t pulse_end;
uint32_t pulse_events;


/* Interrupt handler to measure pulse interval
 */
void __time_critical_func(pulse_measure_callback)(uint gpio, uint32_t events)
{
	if (gpio != pulse_pin || pulse_counter > 1)
		return;

	if (pulse_counter == 0) {
		pulse_start = get_absolute_time();
		pulse_counter++;
	}
	else if (pulse_counter == 1) {
		pulse_end = get_absolute_time();
		measure_complete = true;
		pulse_counter++;
	}
}

/* Setup a GPIO pin to be used for measurements */
void pulse_setup_interrupt(uint gpio, uint32_t events)
{
	pulse_pin = gpio;
	pulse_events = events;
	pulse_counter = 2;
	measure_complete = false;

	gpio_set_irq_enabled_with_callback(pulse_pin, pulse_events, true,
					&pulse_measure_callback);
}

void pulse_disable_interrupt()
{
	gpio_set_irq_enabled(pulse_pin, pulse_events, false);
}

void pulse_enable_interrupt()
{
	gpio_set_irq_enabled(pulse_pin, pulse_events, true);
}

/* Call to start measruement. */
void pulse_start_measure()
{
	pulse_disable_interrupt();
	pulse_counter = 0;
	measure_complete = false;
	pulse_enable_interrupt();
}

/* Call to check if a pulse has been measured yet. */
uint64_t pulse_interval()
{
	uint64_t delta;

	if (!measure_complete)
		return 0;

	/* Calculate pulse length. */
	delta = absolute_time_diff_us(pulse_start, pulse_end);

	return delta;
}


/* eof :-) */
